jakplugg/motivation_radio_hardware/ESP.sch

## EAGLE design ESP.sch (2019-01-18)

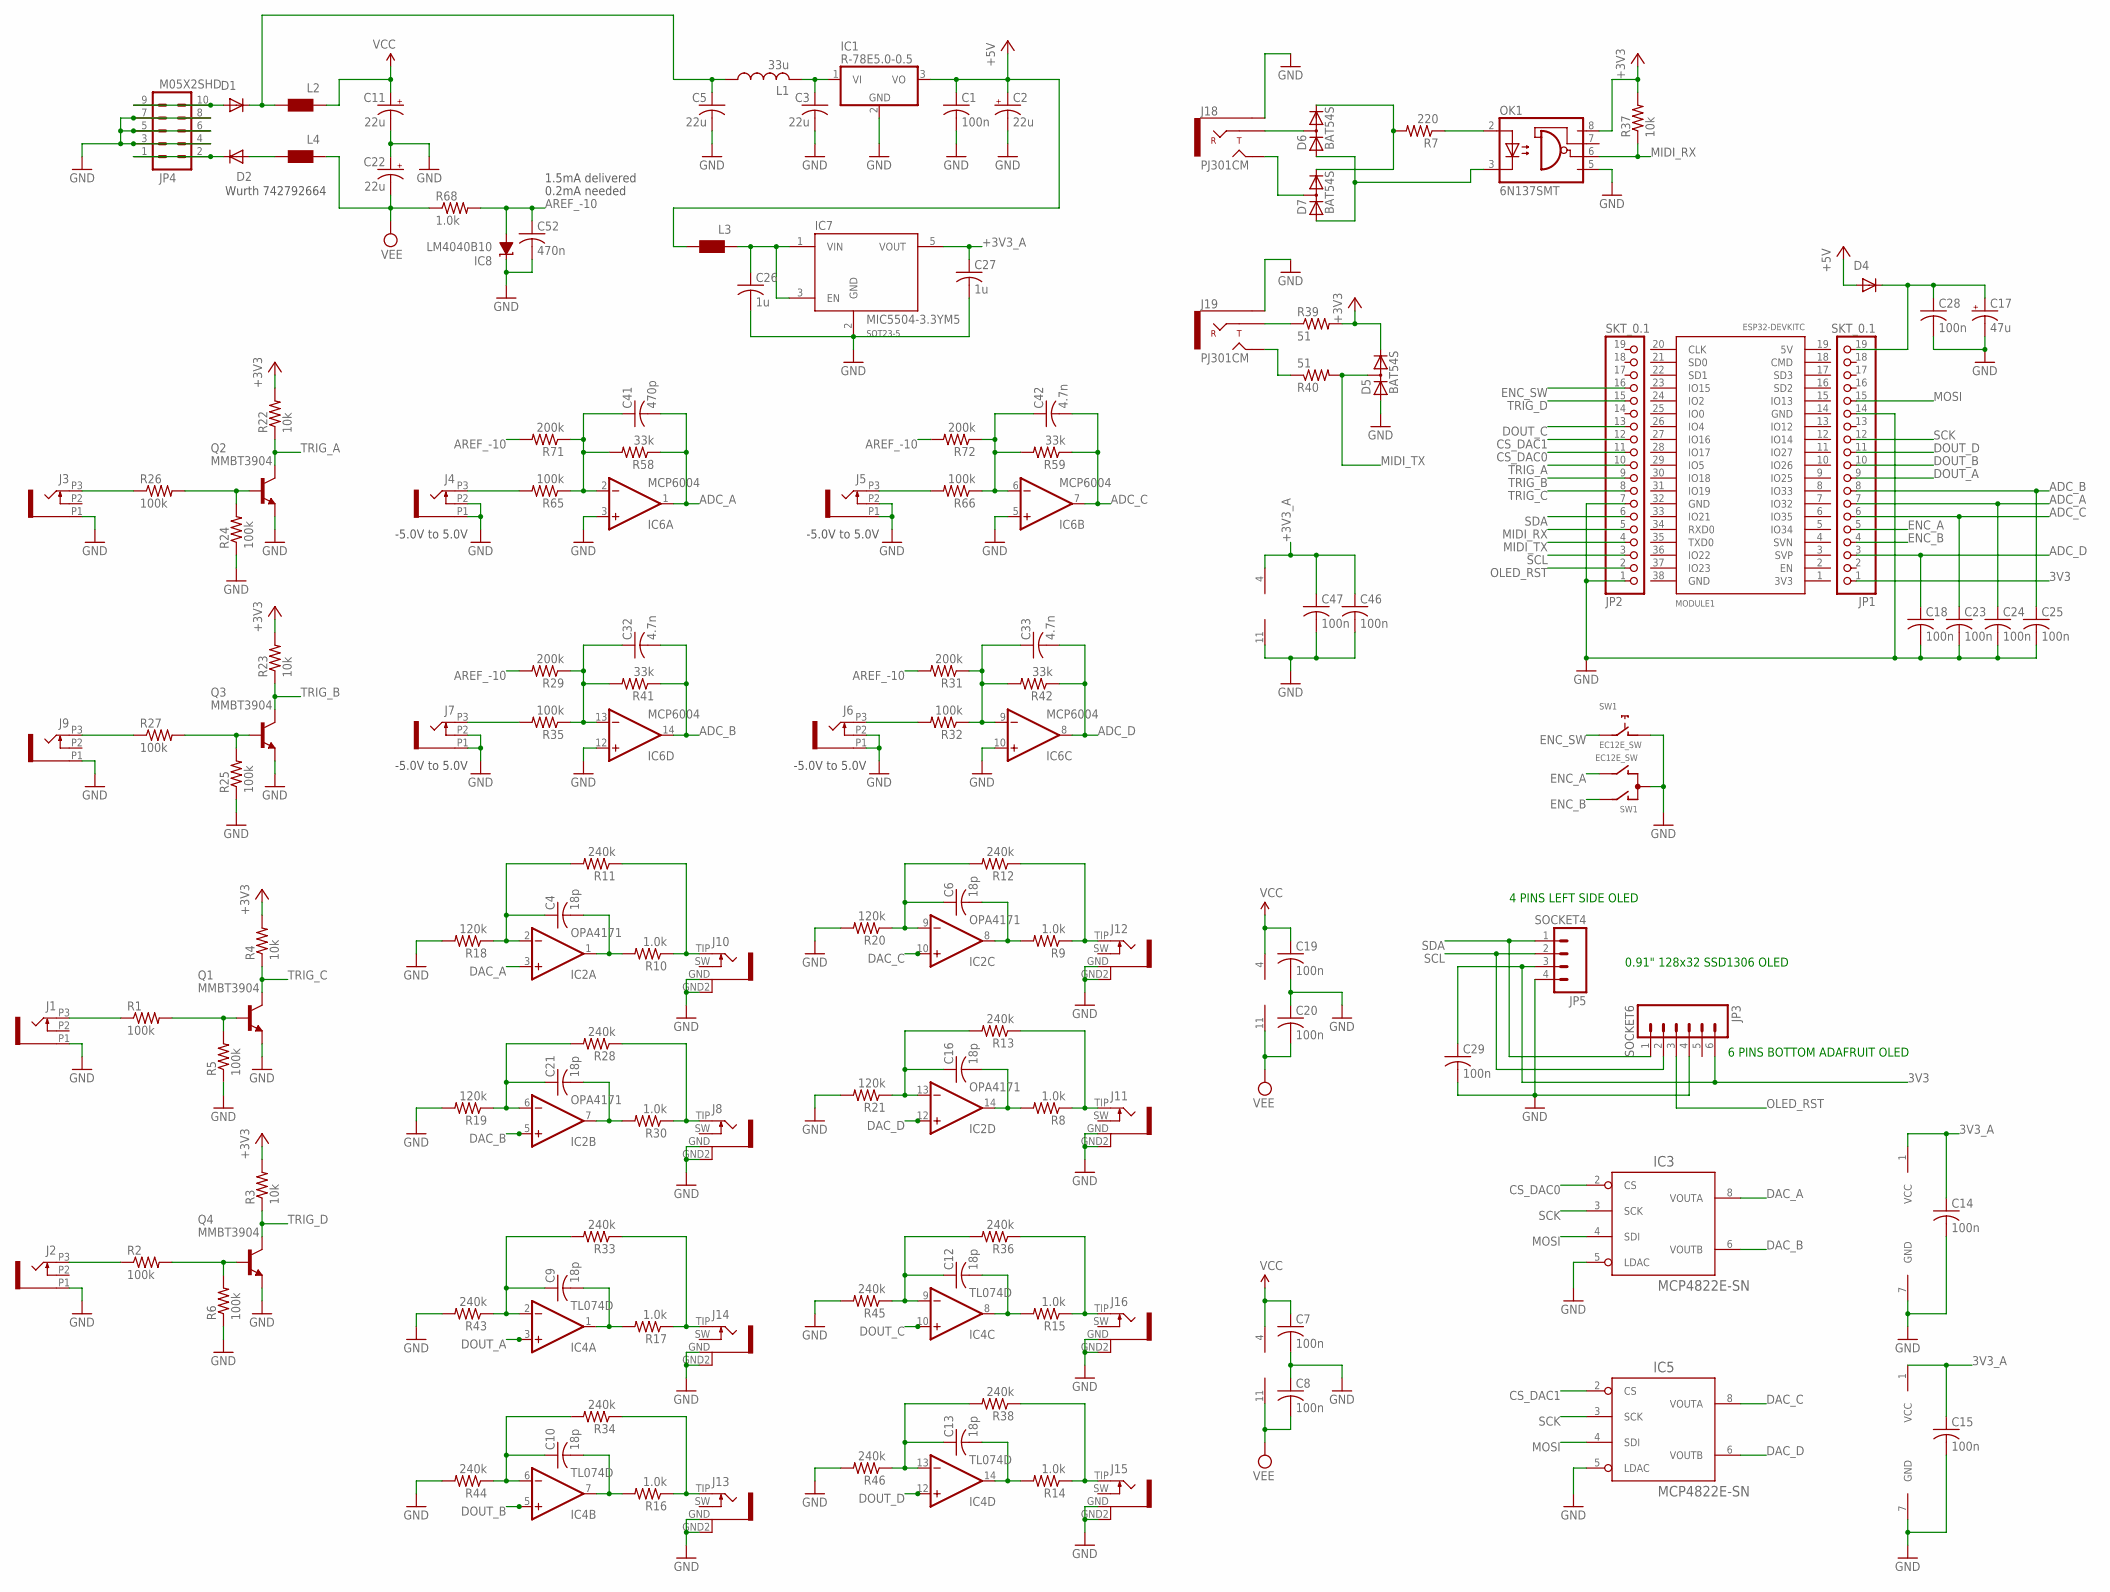
[picture p2: schematic ESP.sch]

Parts:
C1, C18, C23, C24, C25, C28, C46, C47: 100n; C0402
C2, C11, C22: 22u; PANASONIC_C
C3, C5: 22u; C1206
C4, C6, C9, C10, C12, C13, C16, C21: 18p; C0603
C7, C8, C14, C15, C19, C20, C29: 100n; C0603
C17: 47u; PANASONIC_D
C26, C27: 1u; C0603
C32, C33, C42: 4.7n; C0402
C41: 470p; C0402
C52: 470n; C0402
D1, D2, D4: 1N5819HW; SOD123
D5, D6, D7: BAT54S; SOT23
IC1: R-78E5.0-0.5; WE78
IC2: OPA4171; SO14
IC3, IC5: MCP4822E-SN; SOIC-8
IC4: TL074D; SO14
IC6: MCP6004; TSSOP14_065
IC7: MIC5504-3.3YM5; SOT23-5-DBV
IC8: LM4040B10; DBZ_R-PDSO-G3
J1, J2, J3, J4, J5, J6, J7, J9: PJ301_THONKICONN6; WQP_PJ_301M6
J8, J10, J11, J12, J13, J14, J15, J16: PJ301WQP; WQP_PJ_301BM
J18, J19: PJ301CM
JP1, JP2: SKT_0.1; 1X19
JP3: SOCKET6; MOLEX-1X6-RA
JP4: M05X2SHD; 2X5-SHROUDED
JP5: SOCKET4; 1X04
L1: 33u; L2012C
L2, L3, L4: WE-CBF_0603; 0603
MODULE1: ESP32DEVKITC; ESP32-DEVKITC
OK1: 6N137SMT; DIL8-SMD
Q1, Q2, Q3, Q4: MMBT3904; SOT23-BEC
R1, R2, R5, R6, R24, R25, R26, R27, R32, R35, R65, R66: 100k; R0402
R3, R4, R22, R23: 10k; R0402
R7: 220; R0603
R8, R9, R10, R14, R15, R16, R17, R30: 1.0k; R0603
R11, R12, R13, R28, R33, R34, R36, R38, R43, R44, R45, R46: 240k; R0603
R18, R19, R20, R21: 120k; R0603
R29, R31, R71, R72: 200k; R0402
R37: 10k; R0603
R39, R40: 51; R0603
R41, R42, R58, R59: 33k; R0402
R68: 1.0k; R0402
SW1: EC12E_SW; ALPS_EC12E_SW

Connections:
3V3: C29.1, JP1.1, JP3.6, JP5.3
3V3_A: C14.1, C15.1, IC3.1 (VCC), IC5.1 (VCC)
+3V3: D5.2 (C), OK1.8 (VCC), R3.2, R4.2, R22.2, R23.2, R37.2, R39.2
+3V3_A: C27.1, C46.1, C47.1, IC6.4 (V+), IC7.5 (VOUT)
+5V: C1.1, C2.+, D4.A, IC1.3 (VO), L3.2
ADC_A: C24.1, C41.2, IC6.1 (OUT), JP1.7, R58.1
ADC_B: C25.1, C32.2, IC6.14 (OUT), JP1.8, R41.1
ADC_C: C23.1, C42.2, IC6.7 (OUT), JP1.6, R59.1
ADC_D: C18.1, C33.2, IC6.8 (OUT), JP1.3, R42.1
AREF_-10: C52.1, IC8.2 (A), R29.2, R31.2, R68.2, R71.2, R72.2
CS_DAC0: IC3.2 (CS), JP2.11
CS_DAC1: IC5.2 (CS), JP2.12
DAC_A: IC2.3 (+IN), IC3.8 (VOUTA)
DAC_B: IC2.5 (+IN), IC3.6 (VOUTB)
DAC_C: IC2.10 (+IN), IC5.8 (VOUTA)
DAC_D: IC2.12 (+IN), IC5.6 (VOUTB)
DOUT_A: IC4.3 (+IN), JP1.9
DOUT_B: IC4.5 (+IN), JP1.10
DOUT_C: IC4.10 (+IN), JP2.13
DOUT_D: IC4.12 (+IN), JP1.11
ENC_A: JP1.5, SW1.B
ENC_B: JP1.4, SW1.A
ENC_SW: JP2.16, SW1.E (2)
GND: C1.2, C2.-, C3.2, C5.2, C7.2, C8.1, C11.-, C14.2, C15.2, C17.-, C18.2, C19.2, C20.1, C22.+, C23.2, C24.2, C25.2, C26.2, C27.2, C28.2, C29.2, C46.2, C47.2, C52.2, D5.1 (A), IC1.2 (GND), IC3.5 (LDAC), IC3.7 (GND), IC5.5 (LDAC), IC5.7 (GND), IC6.3 (+IN), IC6.5 (+IN), IC6.10 (+IN), IC6.11 (V-), IC6.12 (+IN), IC7.2 (GND), IC8.1 (C), J1.P1 (1), J2.P1 (1), J3.P1 (1), J4.P1 (1), J4.P2 (2), J5.P1 (1), J5.P2 (2), J6.P1 (1), J6.P2 (2), J7.P1 (1), J7.P2 (2), J8.GND (1), J8.GND2 (4), J9.P1 (1), J10.GND (1), J10.GND2 (4), J11.GND (1), J11.GND2 (4), J12.GND (1), J12.GND2 (4), J13.GND (1), J13.GND2 (4), J14.GND (1), J14.GND2 (4), J15.GND (1), J15.GND2 (4), J16.GND (1), J16.GND2 (4), J18.P$1 (EARTH), J19.P$1 (EARTH), JP1.14, JP2.1, JP2.7, JP3.4, JP4.3, JP4.4, JP4.5, JP4.6, JP4.7, JP4.8, JP5.4, OK1.5 (GND), Q1.E, Q2.E, Q3.E, Q4.E, R5.1, R6.1, R18.2, R19.2, R20.2, R21.2, R24.1, R25.1, R43.2, R44.2, R45.2, R46.2, SW1.C, SW1.D (1)
MIDI_RX: JP2.5, OK1.6 (VO), R37.1
MIDI_TX: D5.3 (AC), JP2.4, R40.2
MORPH_IN1: J7.P3 (3), R35.2
MORPH_IN3: J4.P3 (3), R65.2
MORPH_IN5: J6.P3 (3), R32.2
MORPH_IN6: J5.P3 (3), R66.2
MOSI: IC3.4 (SDI), IC5.4 (SDI), JP1.15
unnamed: J3.P3 (3), R26.1
unnamed: J19.P$2 (RING), R39.1
unnamed: D6.3 (AC), J18.P$2 (RING)
unnamed: C26.1, IC7.1 (VIN), IC7.3 (EN), L3.1
unnamed: C41.1, IC6.2 (-IN), R58.2, R65.1, R71.1
unnamed: C5.1, D1.C, L1.1, L2.2
unnamed: D7.3 (AC), J18.P$3 (TIP)
unnamed: D6.2 (C), D7.2 (C), R7.2
unnamed: D2.A, L4.2
unnamed: J1.P3 (3), R1.1
unnamed: C17.+, C28.1, D4.C, JP1.19
unnamed: C42.1, IC6.6 (-IN), R59.2, R66.1, R72.1
unnamed: J2.P3 (3), R2.1
unnamed: Q1.B, R1.2, R5.2
unnamed: Q4.B, R2.2, R6.2
unnamed: D6.1 (A), D7.1 (A), OK1.3 (C)
unnamed: J19.P$3 (TIP), R40.1
unnamed: C32.1, IC6.13 (-IN), R29.1, R35.1, R41.2
unnamed: C33.1, IC6.9 (-IN), R31.1, R32.1, R42.2
unnamed: C3.1, IC1.1 (VI), L1.2
unnamed: J9.P3 (3), R27.1
unnamed: OK1.2 (A), R7.1
unnamed: C21.2, IC2.7 (OUT), R30.2
unnamed: C6.2, IC2.8 (OUT), R9.2
unnamed: C16.2, IC2.14 (OUT), R8.2
unnamed: J10.TIP (2), R10.1, R11.1
unnamed: J12.TIP (2), R9.1, R12.1
unnamed: C4.2, IC2.1 (OUT), R10.2
unnamed: J11.TIP (2), R8.1, R13.1
unnamed: Q2.B, R24.2, R26.2
unnamed: Q3.B, R25.2, R27.2
unnamed: C16.1, IC2.13 (-IN), R13.2, R21.1
unnamed: D1.A, JP4.9, JP4.10
unnamed: D2.C, JP4.1, JP4.2
unnamed: C6.1, IC2.9 (-IN), R12.2, R20.1
unnamed: C21.1, IC2.6 (-IN), R19.1, R28.2
unnamed: C4.1, IC2.2 (-IN), R11.2, R18.1
unnamed: J8.TIP (2), R28.1, R30.1
unnamed: C9.2, IC4.1 (OUT), R17.2
unnamed: C10.2, IC4.7 (OUT), R16.2
unnamed: C12.2, IC4.8 (OUT), R15.2
unnamed: C13.2, IC4.14 (OUT), R14.2
unnamed: J14.TIP (2), R17.1, R33.1
unnamed: J16.TIP (2), R15.1, R36.1
unnamed: J15.TIP (2), R14.1, R38.1
unnamed: C13.1, IC4.13 (-IN), R38.2, R46.1
unnamed: C12.1, IC4.9 (-IN), R36.2, R45.1
unnamed: C10.1, IC4.6 (-IN), R34.2, R44.1
unnamed: C9.1, IC4.2 (-IN), R33.2, R43.1
unnamed: J13.TIP (2), R16.1, R34.1
OLED_RST: JP2.2, JP3.3
SCK: IC3.3 (SCK), IC5.3 (SCK), JP1.12
SCL: JP2.3, JP3.2, JP5.2
SDA: JP2.6, JP3.1, JP5.1
TRIG_A: JP2.10, Q2.C, R22.1
TRIG_B: JP2.9, Q3.C, R23.1
TRIG_C: JP2.8, Q1.C, R4.1
TRIG_D: JP2.15, Q4.C, R3.1
VCC: C7.1, C11.+, C19.1, IC2.4 (V+), IC4.4 (V+), L2.1
VEE: C8.2, C20.2, C22.-, IC2.11 (V-), IC4.11 (V-), L4.1, R68.1

Notes on the sheet:
0.2mA needed
Wurth 742792664
1.5mA delivered
-5.0V to 5.0V
0.91" 128x32 SSD1306 OLED
6 PINS BOTTOM ADAFRUIT OLED
4 PINS LEFT SIDE OLED
